chiayeushyang/MAKER_PI_RO2040/MPU6050/MPU6050.ino

/* Get all possible data from MPU6050
 * Accelerometer values are given as multiple of the gravity [1g = 9.81 m/s²]
 * Gyro values are given in deg/s
 * Angles are given in degrees
 * Note that X and Y are tilt angles and not pitch/roll.
 *
 * License: MIT
 */

#include "Wire.h"
#include <MPU6050_light.h>

MPU6050 mpu(Wire1);

long timer = 0;

void setup() {
  Wire1.setSDA(26);
  Wire1.setSCL(27);
  Serial.begin(9600);
  Wire1.begin();
  
  byte status = mpu.begin();
  Serial.print(F("MPU6050 status: "));
  Serial.println(status);
  while(status!=0){ } // stop everything if could not connect to MPU6050
  
  Serial.println(F("Calculating offsets, do not move MPU6050"));
  delay(1000);
  mpu.calcOffsets(true,true); // gyro and accelero
  Serial.println("Done!\n");
  
}

void loop() {
  mpu.update();

  if(millis() - timer > 1000){ // print data every second
    Serial.print(F("TEMPERATURE: "));Serial.println(mpu.getTemp());
    Serial.print(F("ACCELERO  X: "));Serial.print(mpu.getAccX());
    Serial.print("\tY: ");Serial.print(mpu.getAccY());
    Serial.print("\tZ: ");Serial.println(mpu.getAccZ());
  
    Serial.print(F("GYRO      X: "));Serial.print(mpu.getGyroX());
    Serial.print("\tY: ");Serial.print(mpu.getGyroY());
    Serial.print("\tZ: ");Serial.println(mpu.getGyroZ());
  
    Serial.print(F("ACC ANGLE X: "));Serial.print(mpu.getAccAngleX());
    Serial.print("\tY: ");Serial.println(mpu.getAccAngleY());
    
    Serial.print(F("ANGLE     X: "));Serial.print(mpu.getAngleX());
    Serial.print("\tY: ");Serial.print(mpu.getAngleY());
    Serial.print("\tZ: ");Serial.println(mpu.getAngleZ());
    Serial.println(F("=====================================================\n"));
    timer = millis();
  }

}
